SvenMatzke/PlantMonitor/Assembly/BaseParts/BaseClippedSide.FCStd

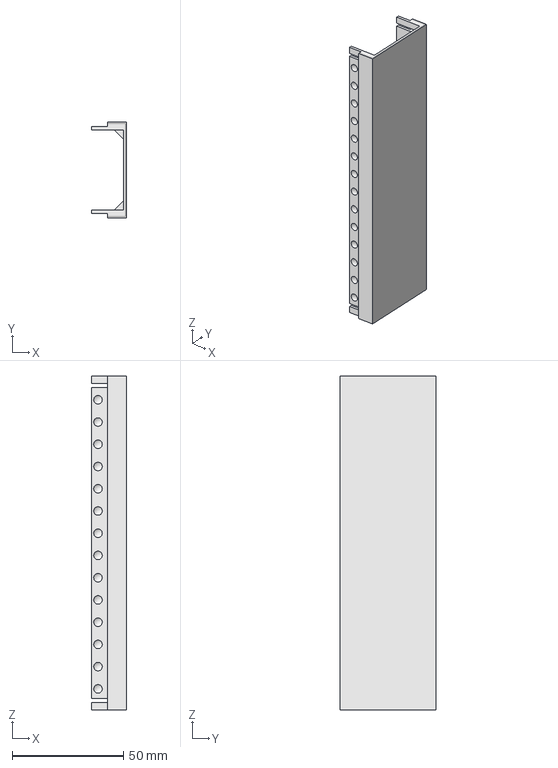
[picture p15: CAD file, 2018-10-18]
Assembly/BaseParts/BaseClippedSide.FCStd
15.9 x 43.0 x 150.2 mm
