SvenMatzke/PlantMonitor/Assembly/BaseParts/BaseRightSide.FCStd

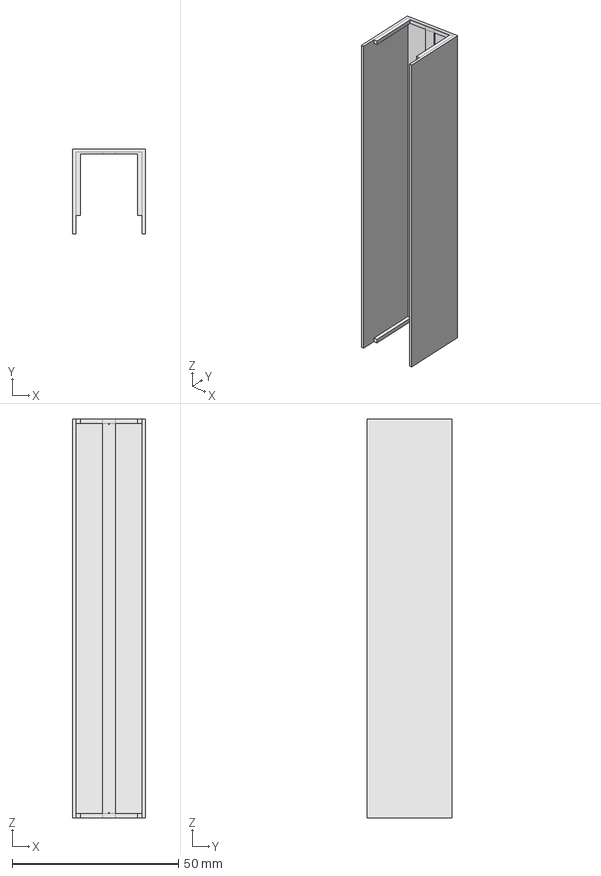
[picture p16: CAD file, 2018-07-12]
Assembly/BaseParts/BaseRightSide.FCStd
22.0 x 25.7 x 120.0 mm
