SvenMatzke/PlantMonitor/Assembly/BaseParts/ESP8266_AiThinkerExpansionHolder.FCStd

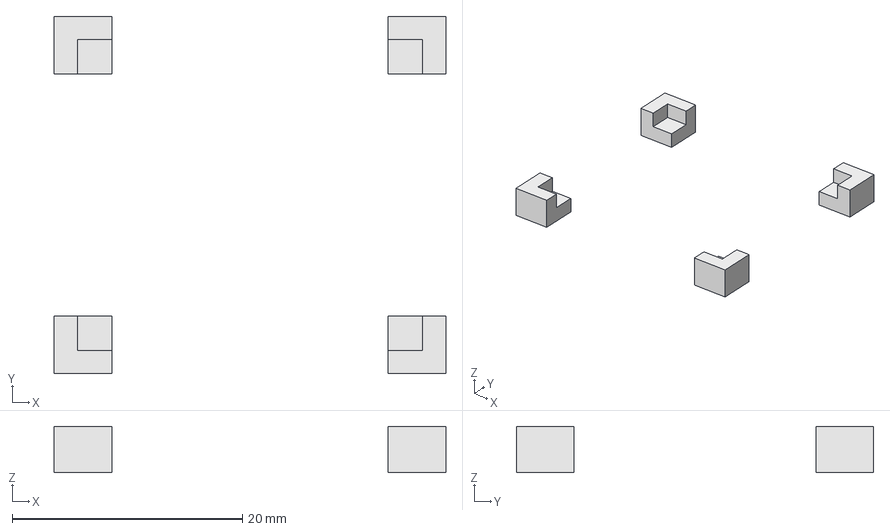
[picture p17: CAD file, 2018-06-11]
Assembly/BaseParts/ESP8266_AiThinkerExpansionHolder.FCStd
34.0 x 31.0 x 4.00 mm
